Aetrius/arduino_water_sensor/secrets.h

#include <pgmspace.h>

#define SECRET

#define WIFI_SSID "XXX"
#define WIFI_PASSWORD "XXX"

// The MQTT topics that this device should publish/subscribe
// Example topic #define MQTT_PUBLISH_TOPIC  "sump_pump_basement"
#define MQTT_PUBLISH_TOPIC  "sump_pump_basement"

#define MQTT_SERVER "192.168.1.X"
#define MQTT_USER "XXXXXXXX"
#define MQTT_PASSWORD "XXXXXXXX"
